eshazen/watch/src/test_7seg/uart.h

#include <avr/io.h>

#include <stdio.h>

#define USART_BAUDRATE 1200
#define UBRR_VALUE (((F_CPU / (USART_BAUDRATE * 16UL))) - 1)

void USART0Init(void);
int USART0SendByte(char u8Data, FILE *stream);
int USART0CharacterAvailable();
int USART0ReceiveByte( FILE *stream);
void USART0GetString( char *buffer, int max);
